oddsocks1024/JACC64-512K/images/3.jpg

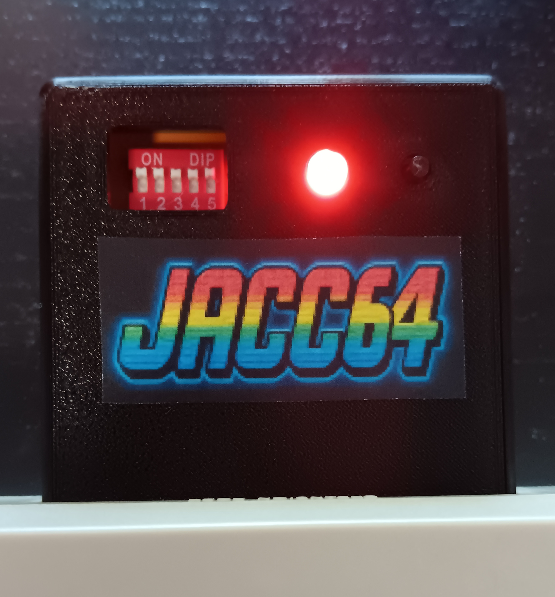
images/3.jpg
